MakersAsylumIS/Team03_Kulfi_Krabs/Documentation/aux_cable_wire_mapping.png

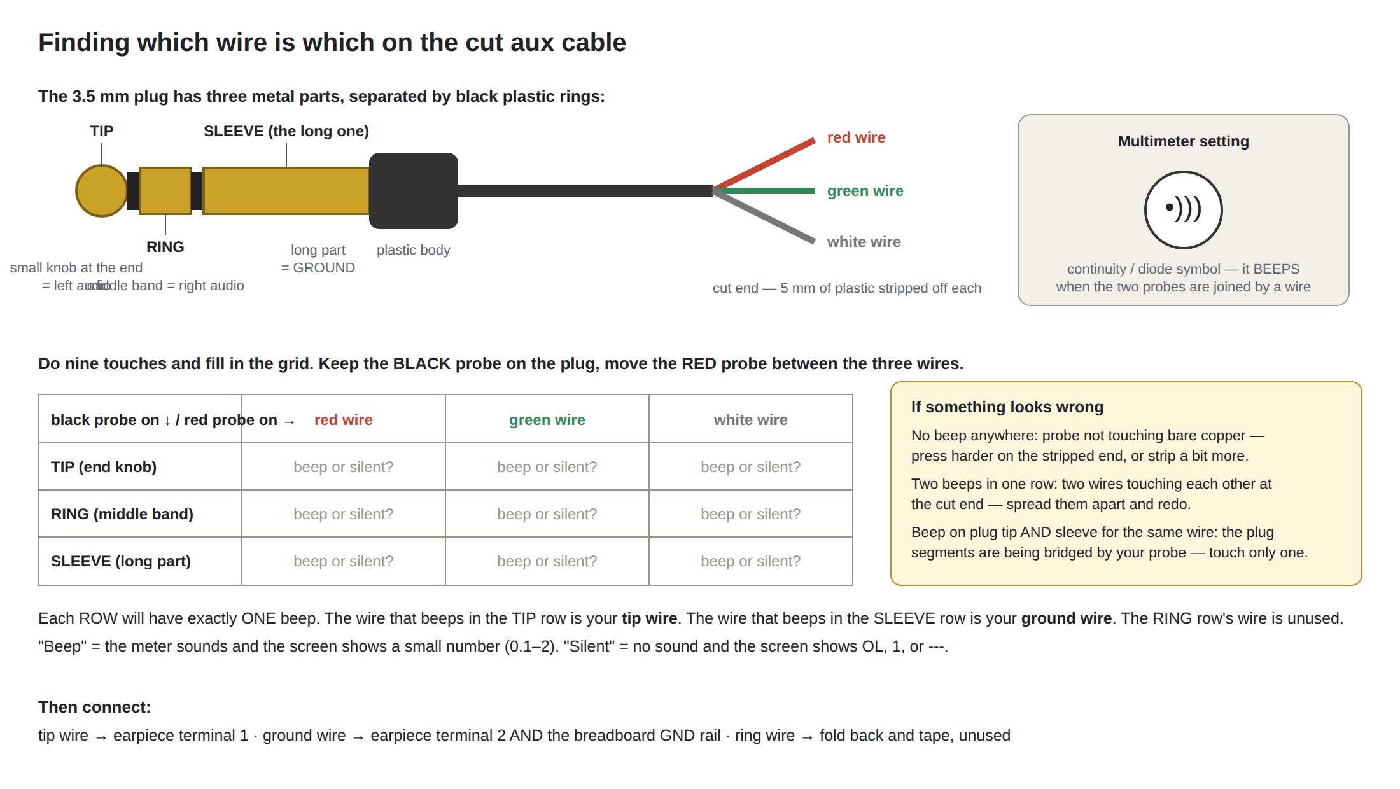
Documentation/aux_cable_wire_mapping.png
