MakersAsylumIS/Team03_Kulfi_Krabs/Reference_Data/02_Microphone_perfboard_as_built.png

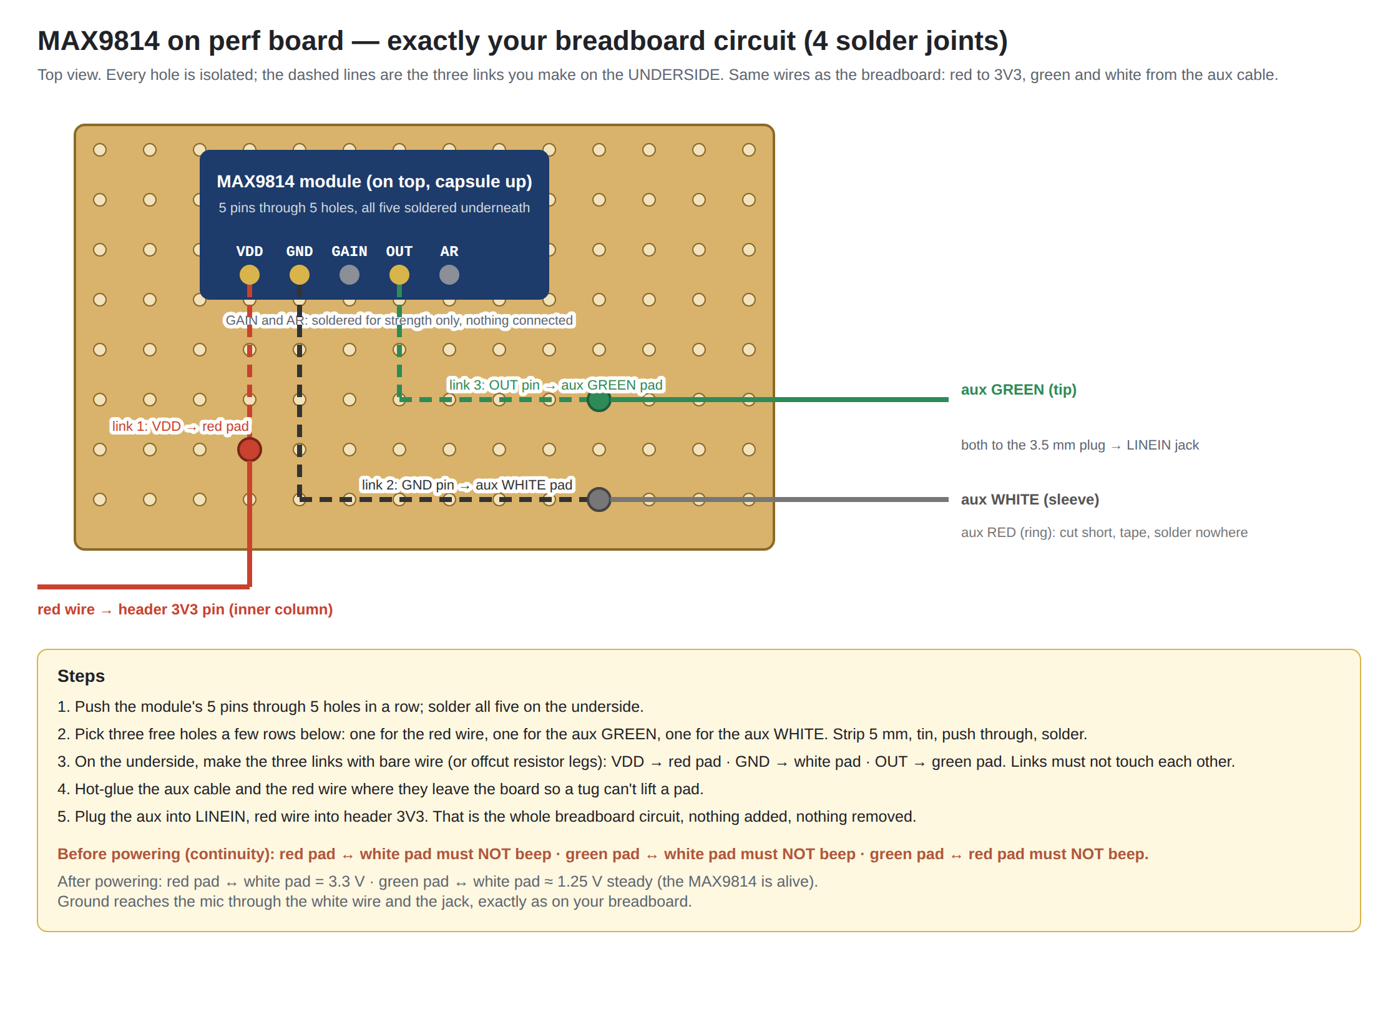
Reference_Data/02_Microphone_perfboard_as_built.png
