MakersAsylumIS/Team03_Kulfi_Krabs/Reference_Data/03_Microphone_perfboard_with_GND_rail_and_keepalive.png

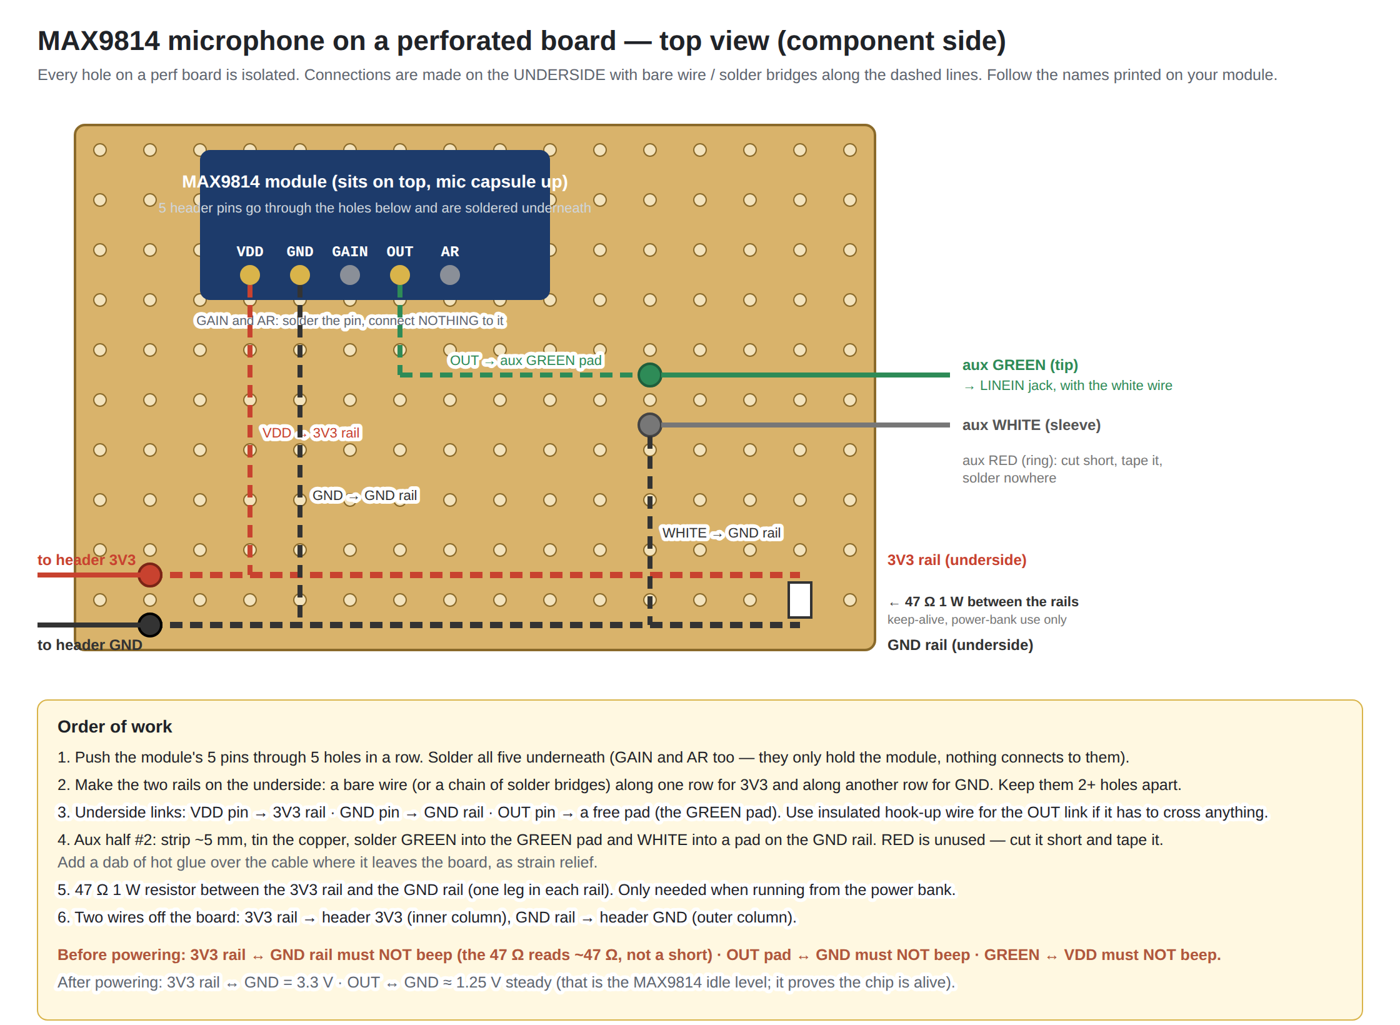
Reference_Data/03_Microphone_perfboard_with_GND_rail_and_keepalive.png
