MakersAsylumIS/Team03_Kulfi_Krabs/Reference_Data/04_TestD_microphone_probe_test.png

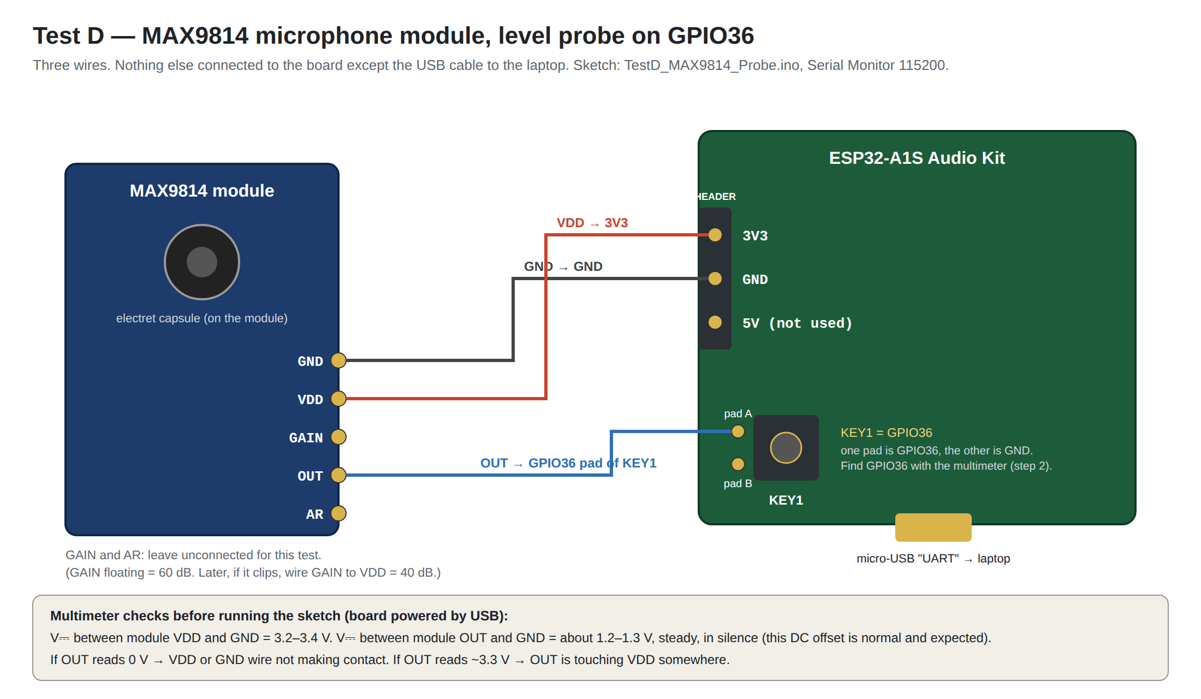
Reference_Data/04_TestD_microphone_probe_test.png
